leaflabs/oak/STM32.sch

## KiCad design STM32.sch (2012-06-29)

Schematic: STM32.sch

Parts:
BUT1, BUT2: BUT
C42, C43: 18pF
D8: LED
JP1: JP_SW
OSC1: 8Mhz
R1: 1.5k
R4: 10k
R17: 1k
U3: STM32F103ZE
