leaflabs/oak/conn.sch

## KiCad design conn.sch (2012-06-29)

Schematic: conn.sch

Parts:
P5, P6, P7, P8: CONN_32
P10: CONN_5X2
P13: CONN_10X2
SD1: SD

Notes on the sheet:
FPGA top
FPGA bottom
STM32 bottom
STM32 top
STM32 JTAG
