leaflabs/oak/fpgabank02.sch

## KiCad design fpgabank02.sch (2012-06-29)

Schematic: fpgabank02.sch

Parts:
BUT4: BUT
C38: 10pF
C62, C63, C64, C65, C66, C67: 1nF
C87, C88, C89, C90, C91, C92: 47nF
D12: LED
R3: 10
R42: 1k
U4: XC3S250EPQ208; xilinx_devices-PQ208
