leaflabs/oak/fpgabank13.sch

## KiCad design fpgabank13.sch (2012-06-29)

Schematic: fpgabank13.sch

Parts:
C56, C57, C58, C59, C60, C61: 1nF
C81, C82, C83, C84, C85, C86: 47nF
R15: 10k
U4: XC3S250EPQ208; xilinx_devices-PQ208

Notes on the sheet:
-rupt lines
STM32 inter-
