leaflabs/oak/fpgajtag.sch

## KiCad design fpgajtag.sch (2012-06-29)

Schematic: fpgajtag.sch

Parts:
BUT3: BUT
C19, C20, C21: 0.1uF
D6: DONE
P4: CONN_2
P9: CONN_3X2
P12: CONN_6
R8, R9, R10, R11, R12, R13, R39: 10k
R23, R24, R25: 200
R31, R32: 4.7k
R33: 330
U1: DG4053A
U5: XCF04S
