leaflabs/oak/misc.sch

## KiCad design misc.sch (2012-06-29)

Schematic: misc.sch

Parts:
C5, C6, C7, C8, C9, C10, C11, C12, C13, C14, C15, C16, C17, C18: 0.1uF
C29, C30: 0.47uF
C40, C41: 10uF
C44, C45, C46, C47, C48, C49, C50, C51, C52, C53, C54, C55: 1nF
C69, C70, C71, C72, C73, C74, C75, C76, C77, C78, C79, C80: 47nF
C93, C94: 47pF
OSC2: XOSC_SOCKET
OSC3: XOSC
Q3, Q4: NPN
R2, R40, R41: 1.5k
R7: 10k
R21: 1k
R26, R27: 22
R29: 36k
R34: 47k
R43, R44, R45: 100
U4: XC3S250EPQ208; xilinx_devices-PQ208
USB1: USB

Notes on the sheet:
VCCINT bypass caps
VCCAUX bypass caps
STM32 bypass caps
