leaflabs/oak/pwr.sch

## KiCad design pwr.sch (2012-06-29)

Schematic: pwr.sch

Parts:
C1, C2, C3: 0.1uF
C31, C32, C33: 1.5nF
C34, C35, C36: 100uF
C37: 10pF
C39: 10uF
C68: 1uF
D4, D5: DIODE
D9: Power
IC1: TPS75003
L1: 5uH
L2: 15uH
P1: CONN_3
P2: CONN_2
P11: CONN_6
PWR_JACK1: PWR_JACK
Q1, Q2: MOSFET_P
R16: 154k
R22: 2.2k
R28: 365k
R30: 390
R35, R36: 47m
R37, R38: 619k
S1: SWITCH
