leaflabs/oak/sdram.sch

## KiCad design sdram.sch (2012-06-29)

Schematic: sdram.sch

Parts:
C22, C23, C24, C25, C26, C27, C28: 0.1uF
U2: MT48LC16M
